Maker-Gitsune/The-Splaynck/images/IMG-5246.jpg

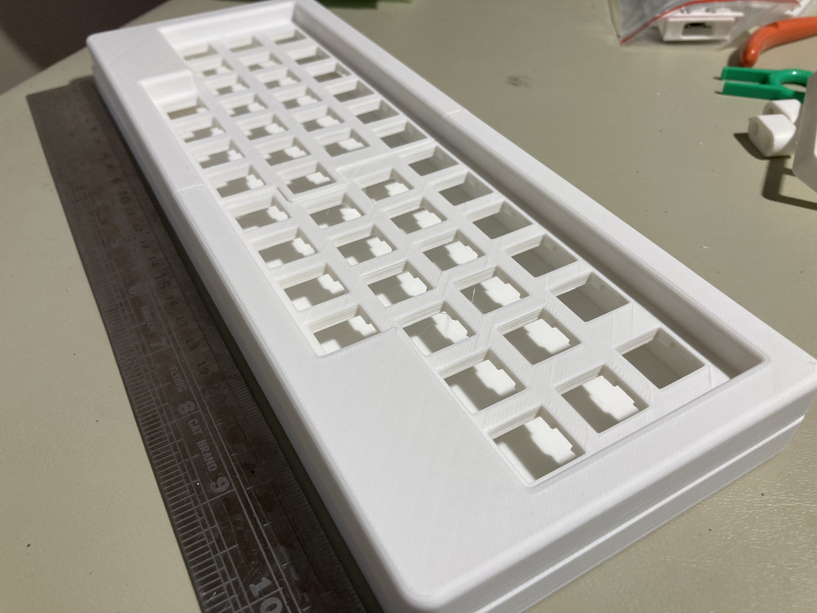
images/IMG-5246.jpg
